ukmaker/BassMate/assets/IMG_1075.JPG

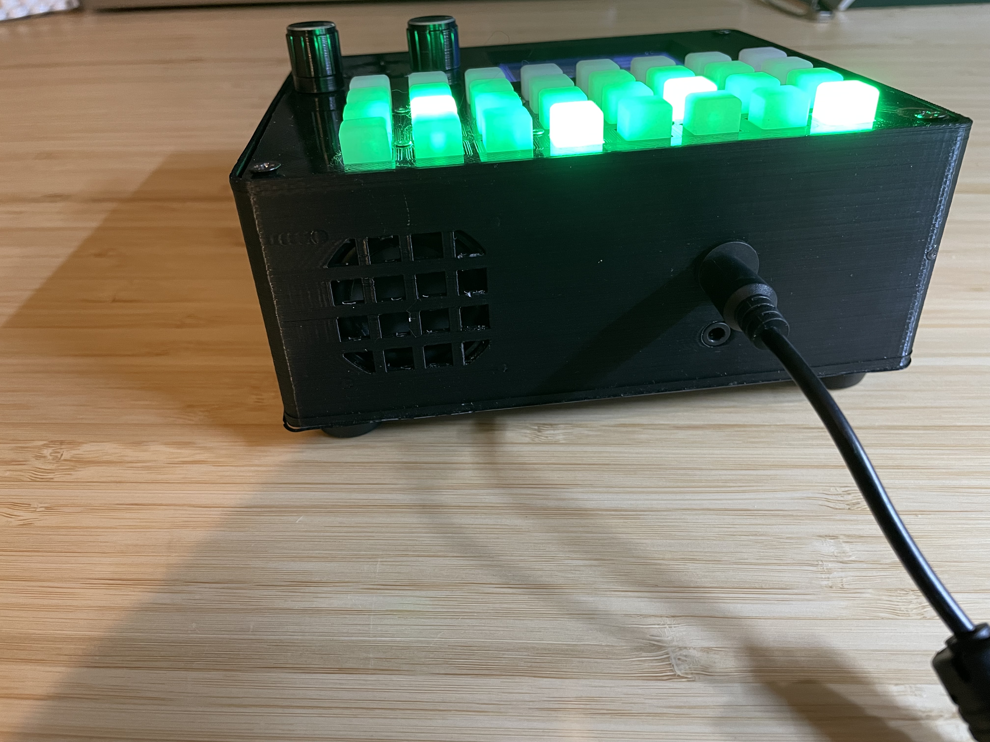
assets/IMG_1075.JPG
